AndersBNielsen/SimpleModem/InitialSketch2.png

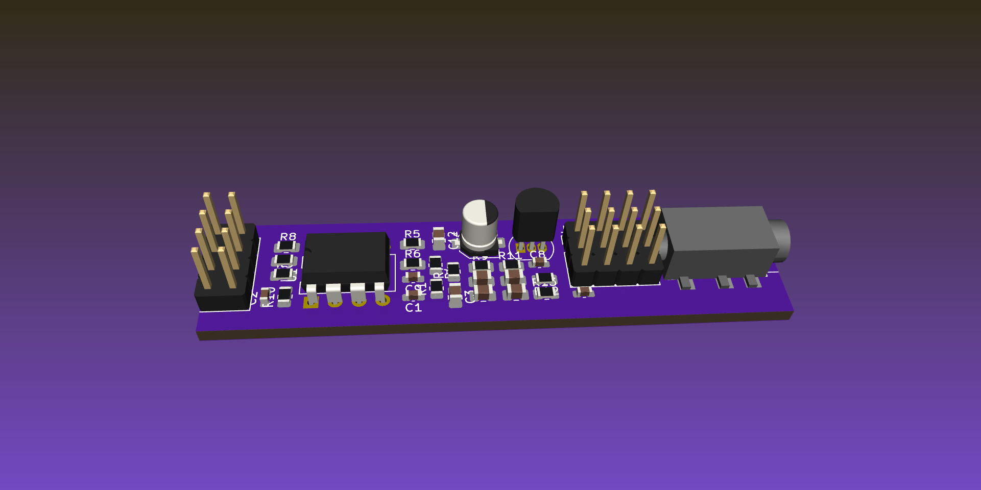
InitialSketch2.png
