AndersBNielsen/SimpleModem/Photos/Resized/IMG_4571.jpeg

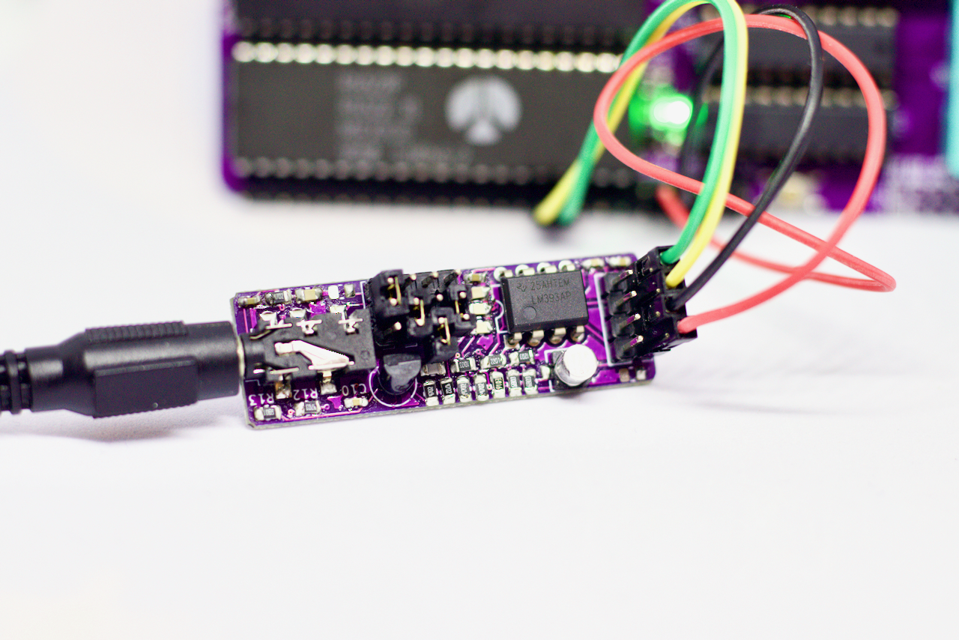
Photos/Resized/IMG_4571.jpeg
