AndersBNielsen/SimpleModem/Photos/Resized/IMG_4609.jpeg

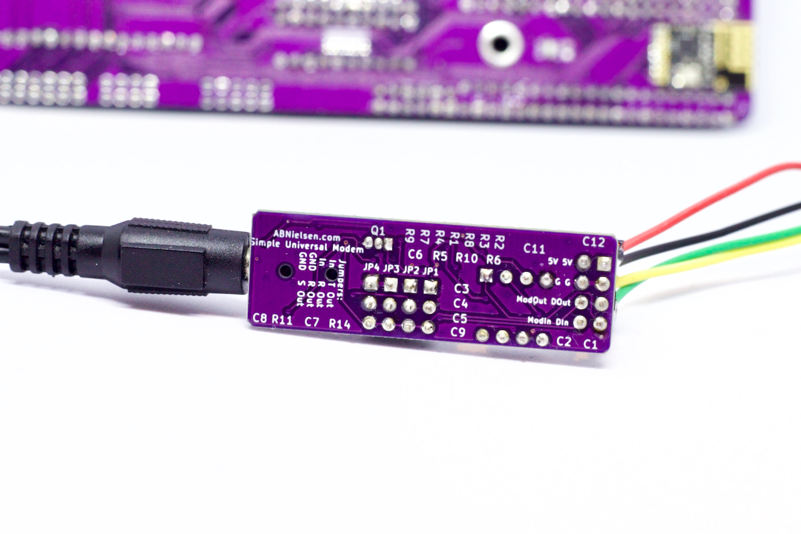
Photos/Resized/IMG_4609.jpeg
