AndersBNielsen/SimpleModem/Photos/Resized/IMG_4610.jpeg

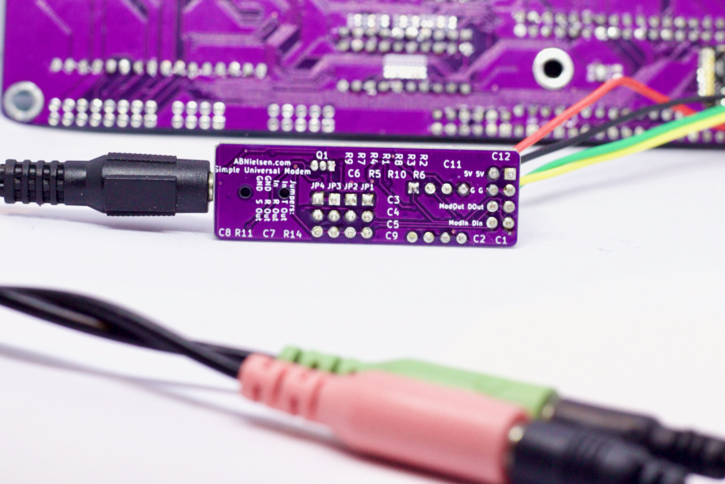
Photos/Resized/IMG_4610.jpeg
