AndersBNielsen/SimpleModem/Photos/Resized/IMG_4613.jpeg

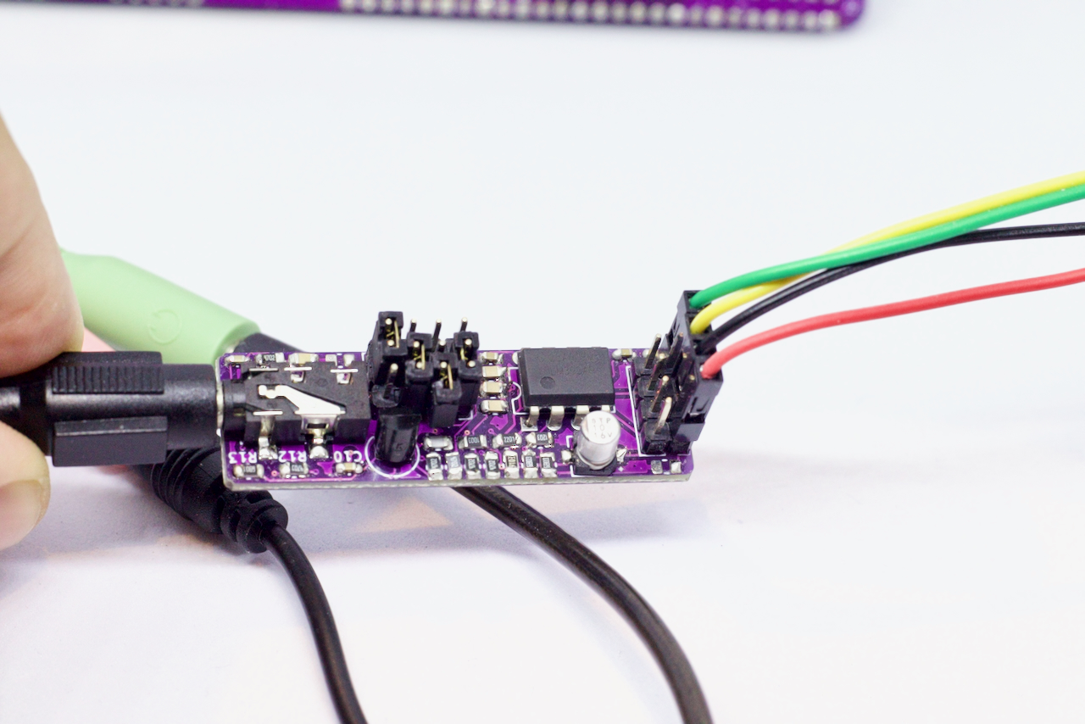
Photos/Resized/IMG_4613.jpeg
