AndersBNielsen/SimpleModem/Photos/Resized/IMG_4616.jpeg

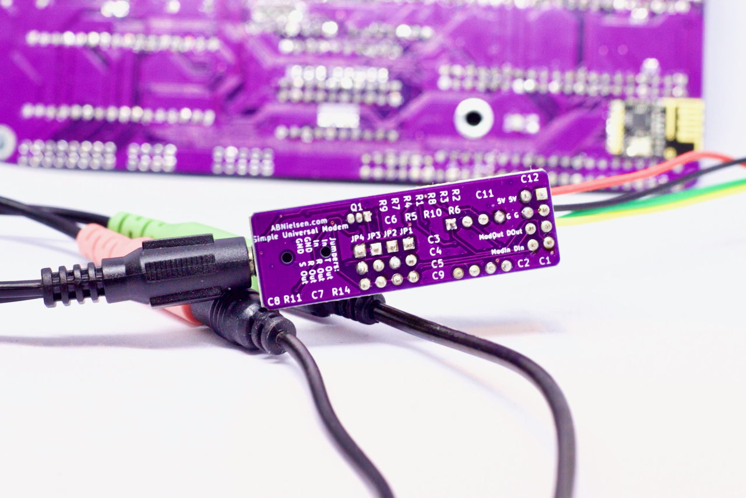
Photos/Resized/IMG_4616.jpeg
