AndersBNielsen/SimpleModem/Photos/Resized/IMG_4663.jpeg

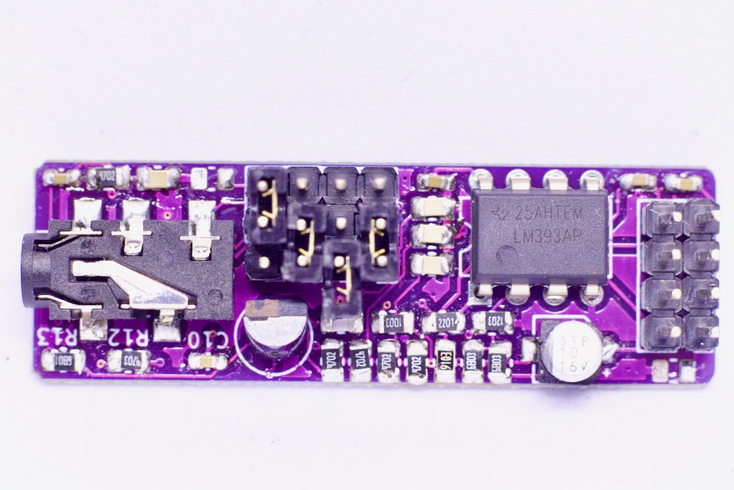
Photos/Resized/IMG_4663.jpeg
