AndersBNielsen/SimpleModem/Photos/Resized/IMG_4670.jpeg

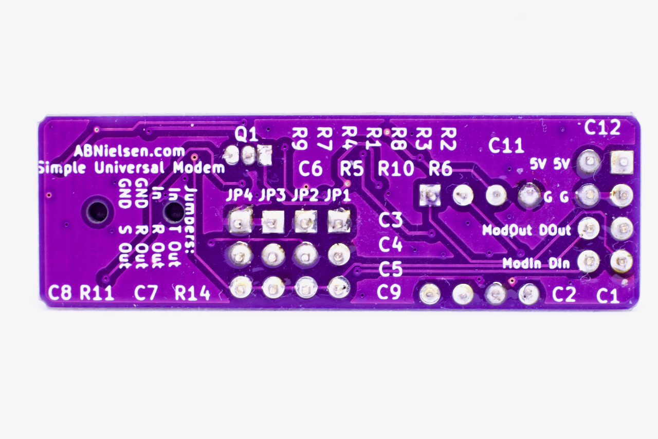
Photos/Resized/IMG_4670.jpeg
