AndersBNielsen/SimpleModem/Photos/Resized/IMG_4686.jpeg

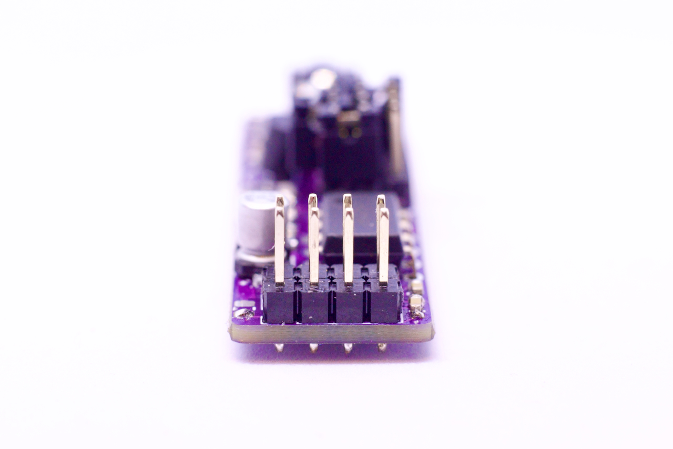
Photos/Resized/IMG_4686.jpeg
