AndersBNielsen/SimpleModem/Photos/Resized/IMG_4688.jpeg

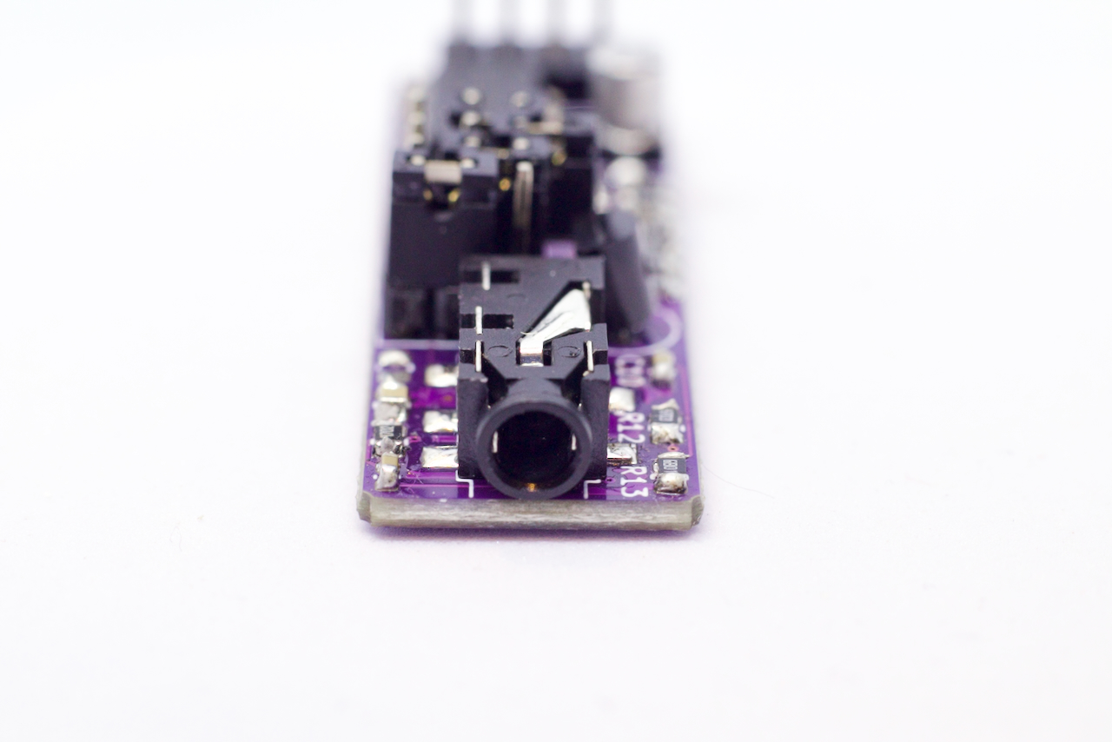
Photos/Resized/IMG_4688.jpeg
