AndersBNielsen/SimpleModem/Photos/Resized/IMG_4689.jpeg

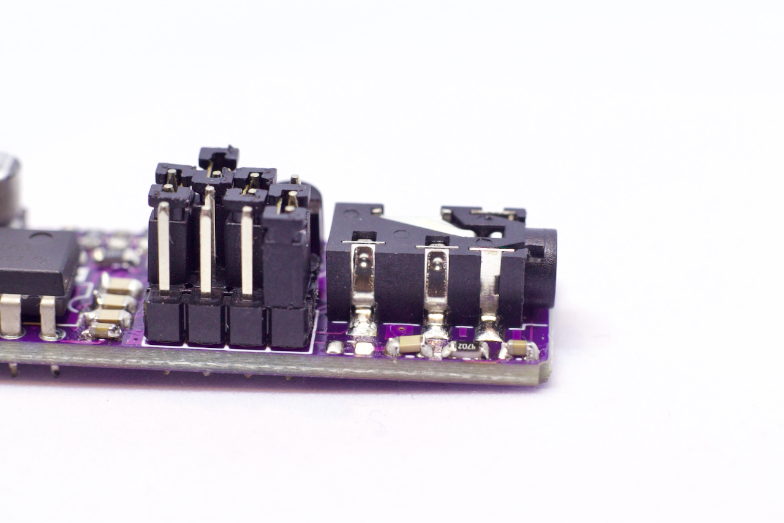
Photos/Resized/IMG_4689.jpeg
